SolderedElectronics/Display-OLED-I2C-Blue-0.96-hardware-design/OUTPUTS/V1.2.2/Display OLED I2C Blue 0.96 SSD1306 Pinout.jpg

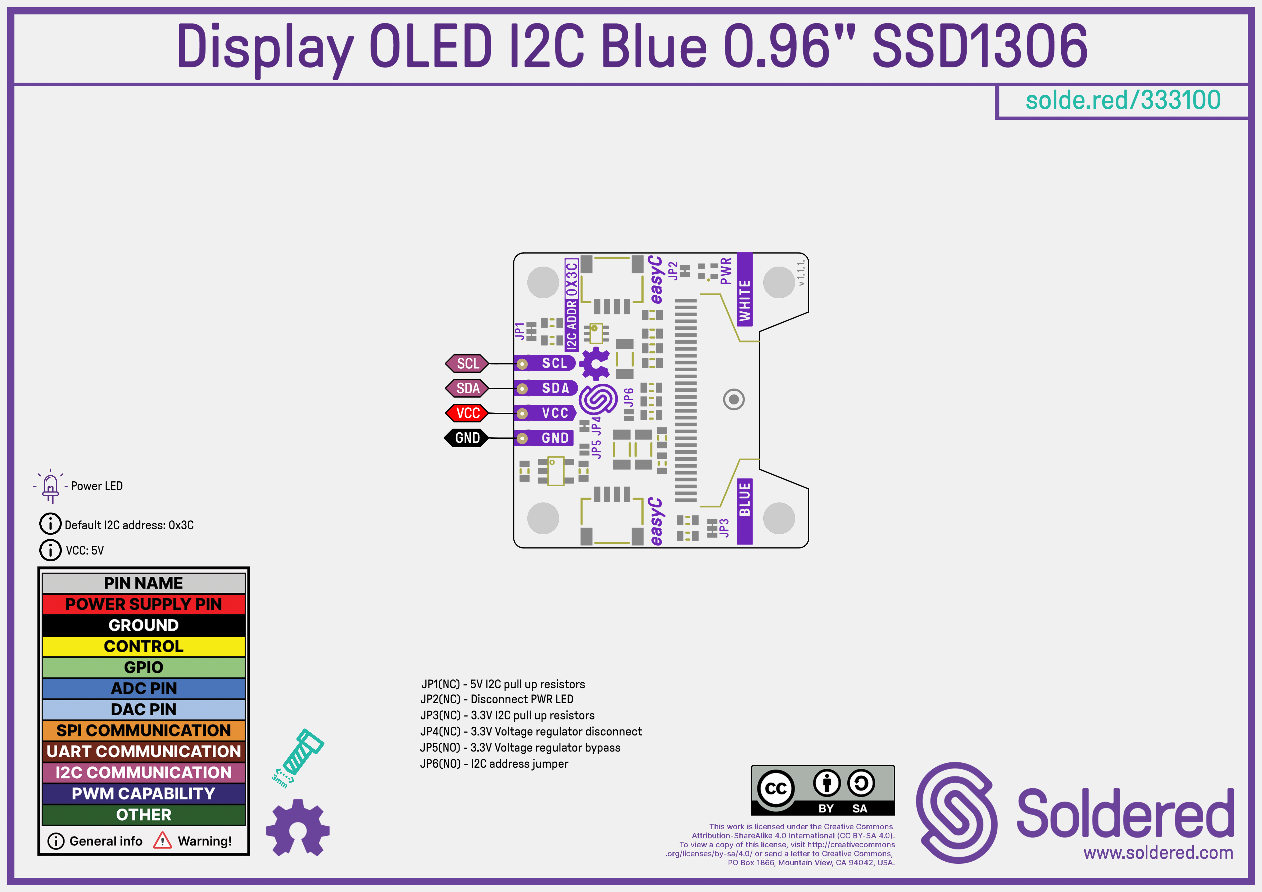
OUTPUTS/V1.2.2/Display OLED I2C Blue 0.96 SSD1306 Pinout.jpg
